TheDIYGuy999/RC_Decoder_4_Channel/2.jpg

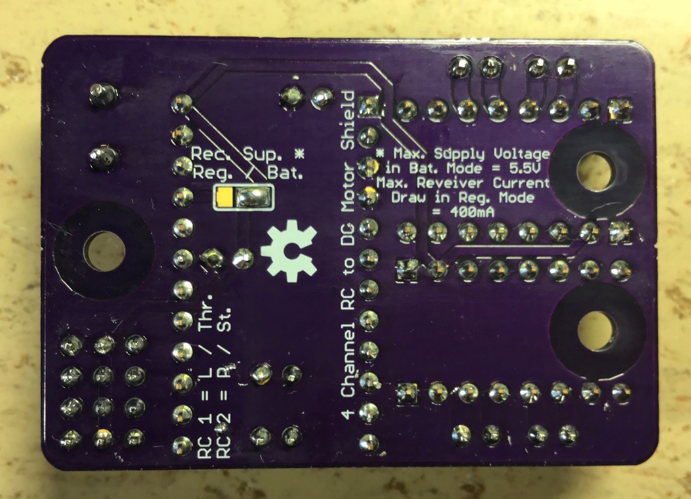
2.jpg
