TheDIYGuy999/RC_Decoder_4_Channel/3.jpg

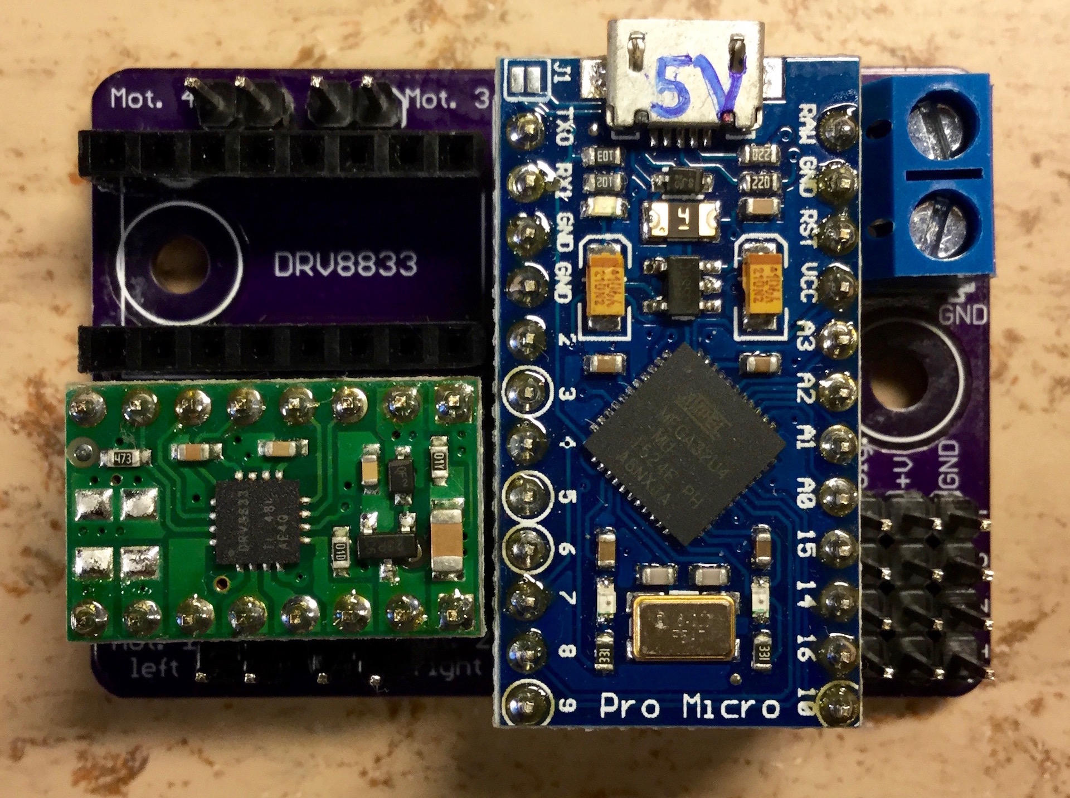
3.jpg
