TheDIYGuy999/RC_Decoder_4_Channel/4.jpg

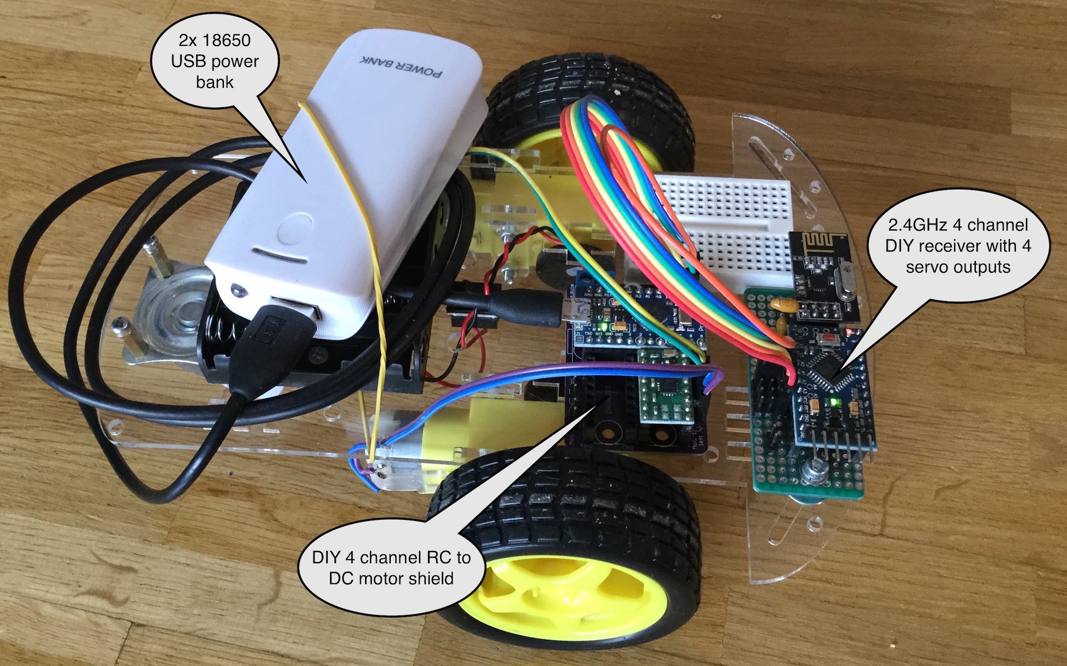
4.jpg
