TheDIYGuy999/RC_Decoder_4_Channel/curves.h

//
// =======================================================================================================
// NONLINEAR ARRAYS FOR STEERING OVERLAY
// =======================================================================================================
//

// In order to optimize the steering behaviour for your vehicle, just change the steering curves in the arrays below

// This array is intended for the "Semi caterpillar" mode. The inner wheel can max. slow down to 60% of the
// outer wheels RPM
float curveSemi[][2] = {  // see excel sheet!
  {0, 60} // {input value, output value}
  , {25, 70}
  , {50, 80}
  , {75, 90}
  , {100, 100}
};

// This array is intended for the "Caterpillar" mode. The inner wheel can spin backwars  up to 100% of the
// outer wheels RPM. That allows for turning the vehicle "on place"
float curveFull[][2] = {
  {0, -100} // {input value, output value}
  , {7, 0}
  , {20, 45}
  , {60, 85}
  , {100, 100}
};

//
// =======================================================================================================
// ARRAY INTERPOLATION
// =======================================================================================================
//

// Credit: http://interface.khm.de/index.php/lab/interfaces-advanced/nonlinear-mapping/

int reMap(float pts[][2], int input) {
  int rr;
  float bb, mm;

  for (int nn = 0; nn < 5; nn++) {
    if (input >= pts[nn][0] && input <= pts[nn + 1][0]) {
      mm = ( pts[nn][1] - pts[nn + 1][1] ) / ( pts[nn][0] - pts[nn + 1][0] );
      mm = mm * (input - pts[nn][0]);
      mm = mm +  pts[nn][1];
      rr = mm;
    }
  }
  return (rr);
}
